TryBreakFixAgain/USBvalve-tbfa-Mod/pictures/usbvalvelipo03.jpg

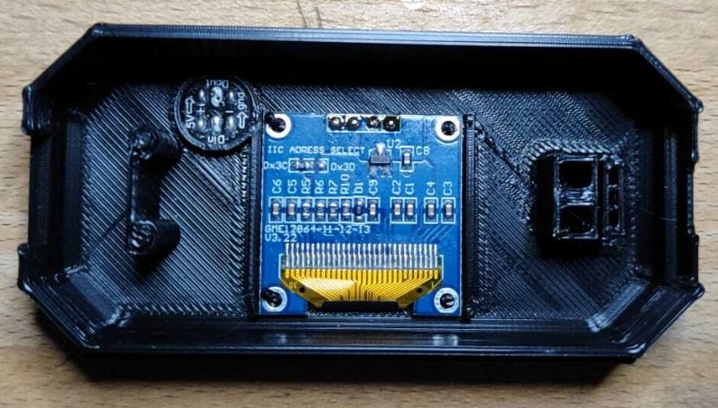
pictures/usbvalvelipo03.jpg
