TryBreakFixAgain/USBvalve-tbfa-Mod/pictures/usbvalvelipo04.jpg

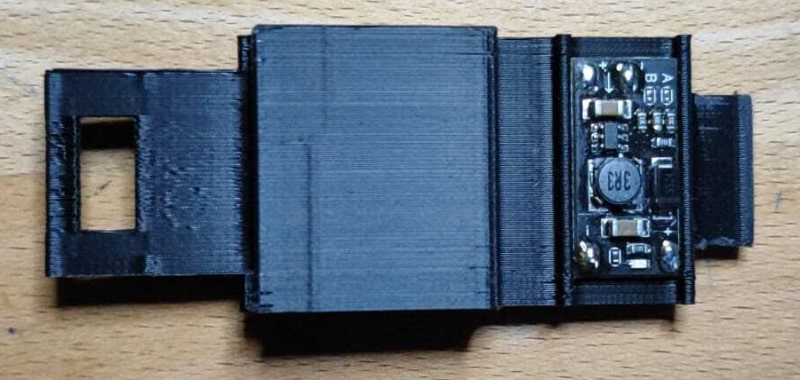
pictures/usbvalvelipo04.jpg
