TryBreakFixAgain/USBvalve-tbfa-Mod/pictures/usbvalvelipo06.jpg

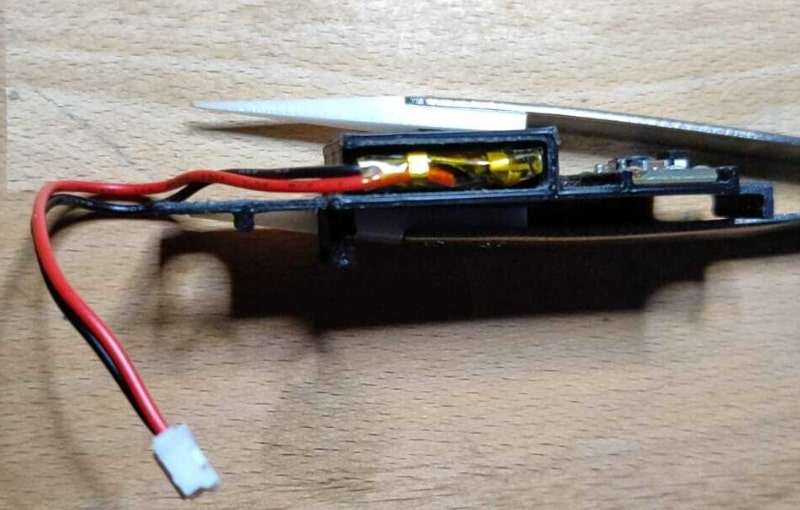
pictures/usbvalvelipo06.jpg
