TryBreakFixAgain/USBvalve-tbfa-Mod/pictures/usbvalvelipo08.jpg

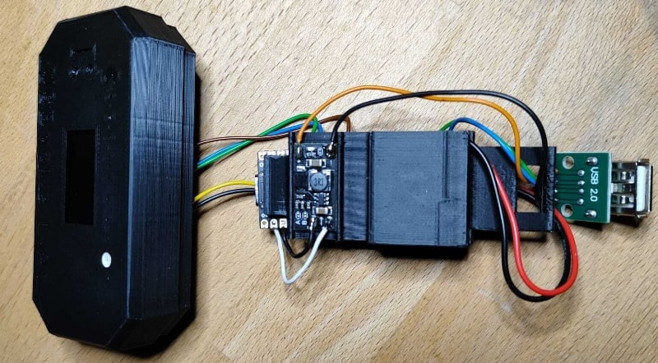
pictures/usbvalvelipo08.jpg
