TryBreakFixAgain/USBvalve-tbfa-Mod/pictures/usbvalvelipo10.jpg

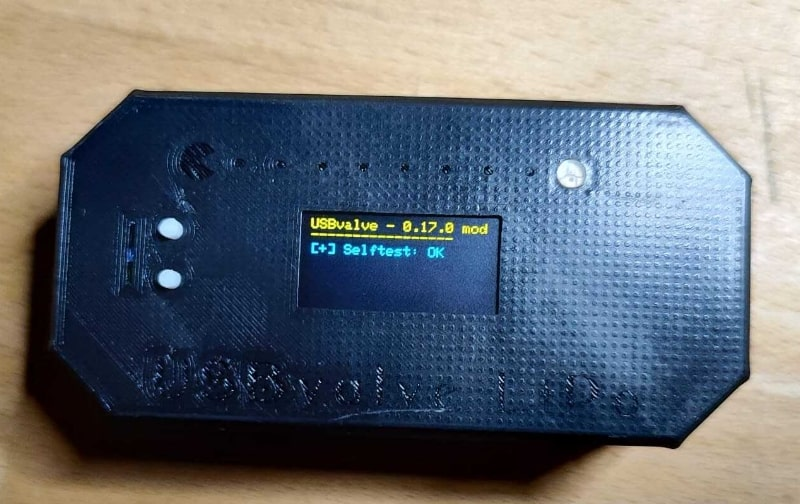
pictures/usbvalvelipo10.jpg
